garthwebb/plant-monitor/sensor/sensor-avr/radioPinFunctions.h

//
// Created by Garth Webb on 11/16/19.
//

#ifndef PLANT_SENSOR_RADIOPINFUNCTIONS_H
#define PLANT_SENSOR_RADIOPINFUNCTIONS_H

#include <stdint.h>

/* -------------------------------------------------------------------------- */
/* In this function you should do the following things:
 *    - Set MISO pin input
 *    - Set MOSI pin output
 *    - Set SCK pin output
 *    - Set CSN pin output
 *    - Set CE pin output     */
/* -------------------------------------------------------------------------- */
void nrf24_setupPins(void);

/* -------------------------------------------------------------------------- */
/* nrf24 CE pin control function
 *    - state:1 => Pin HIGH
 *    - state:0 => Pin LOW     */
/* -------------------------------------------------------------------------- */
void nrf24_ce_digitalWrite(uint8_t state);

/* -------------------------------------------------------------------------- */
/* nrf24 CE pin control function
 *    - state:1 => Pin HIGH
 *    - state:0 => Pin LOW     */
/* -------------------------------------------------------------------------- */
void nrf24_csn_digitalWrite(uint8_t state);

/* -------------------------------------------------------------------------- */
/* nrf24 SCK pin control function
 *    - state:1 => Pin HIGH
 *    - state:0 => Pin LOW     */
/* -------------------------------------------------------------------------- */
void nrf24_sck_digitalWrite(uint8_t state);

/* -------------------------------------------------------------------------- */
/* nrf24 MOSI pin control function
 *    - state:1 => Pin HIGH
 *    - state:0 => Pin LOW     */
/* -------------------------------------------------------------------------- */
void nrf24_mosi_digitalWrite(uint8_t state);

/* -------------------------------------------------------------------------- */
/* nrf24 MISO pin read function           */
/* - returns: Non-zero if the pin is high */
/* -------------------------------------------------------------------------- */
uint8_t nrf24_miso_digitalRead(void);

#endif //PLANT_SENSOR_RADIOPINFUNCTIONS_H
